sooda/thesis/latex/tex/syms-opers-abbrs.tex

\mysection{Symbols and abbreviations}

\subsection*{Symbols}

In general, bold capital letters (e.g., $\bm A$) represent matrices, plain capital letters represent 3D points and corresponding lowercase letters matching 2D points (e.g., $\vec P$, $\vec p$).
The arrow denotes a vector.
Plain letters without the arrow represent scalars.

\begin{tabular}{ll}
	$\vec C$ & camera position\\
	$f$ & focal length\\
	$\kappa_i$ & $i$th radial distortion coefficient\\
	$\bm K$ & camera intrinsic matrix\\
	$\bm M$ & projection matrix\\
	$\bm O$ & coordinate system origin\\
	$\vec p = (p_x, p_y)$ & pixel coordinates matching $\vec P$\\
	$\vec P = (P_x, P_y, P_z)$ & 3D world coordinates\\
	$\rho_i$ & $i$th tangential distortion coefficient\\
	$r$ & radius\\
	$\bm R$ & rotation matrix\\
	$t$ & time\\
	$\bm T$ & translation matrix\\
	$\vec T$ & translation vector\\
\end{tabular}
%
%\subsection*{Operators}
%
%\begin{tabular}{ll}
%$\sum_i $                        & sum over all indices $i$\\
%$\mathbf{a} \cdot \mathbf{b}$    & Dot product of the vectors $\mathbf{a}$ and $\mathbf{b}$
%\end{tabular}

\subsection*{Abbreviations}

\begin{tabular}{ll}
	2D & two-dimensional\\
	3D & three-dimensional\\
	API & Application programming interface\\
	APS-C & Advanced Photo System type-C\\
	b & bit\\
	B & byte\\
	BRDF & Bidirectional reflectance distribution function\\
	CCD & Charge-coupled device\\
	CG & Computer graphics\\
	CMOS & Complementary metal-oxide semiconductor\\
	COC & Circle of confusion\\
	CPU & Central processing unit\\
	DOF & Depth of field\\
	DSLR & Digital SLR\\
	Exif & Exchangeable image file format\\
	FPS & Frames per second\\
	GCC & Gnu compiler collection\\
	GPU & Graphics processing unit\\
	I/O & Input/Output\\
	IC & Integrated circuit\\
	LED & Light-emitting diode\\
	MCU & Microcontroller unit\\
	MILC & Mirrorless interchangeable-lens camera\\
	ML & Magic Lantern\\
	Mocap & Motion capture\\
	MP & Megapixels\\
	MTF & Modulation transfer function\\
	MV & Machine vision\\
	MVS & Multi-view stereo\\
	OpenGL & Open Graphics Library\\
	PCB & Printed circuit board\\
	PCL & Point Cloud Library\\
	px & pixel\\
	RAM & Random-access memory\\
	RGB & Red-green-blue\\
	SD & Secure Digital\\
	SDK & Software development kit\\
	SfM & Structure from motion\\
	SIFT & Scale-invariant feature transform\\
	SLR & Single-lens reflex camera (system camera)\\
	UI & User interface\\
	USB & Universal Serial Bus\\
\end{tabular}
