sooda/thesis/src/gphoto-tether/interesting-settings.txt

# this file is manually processed from --list-all-config
# the lines starting with / are special, used with readconfig.sh. they
# are the ones that are rewritten to other cameras from the selected cam

#/main/settings/capturetarget
#Label: Capture Target
#Type: RADIO
#Current: Internal RAM
#Choice: 0 Internal RAM
#Choice: 1 Memory card

/main/imgsettings/imageformat
Label: Image Format
Type: RADIO
Current: Smaller JPEG (S2)
Choice: 0 Large Fine JPEG
Choice: 1 Large Normal JPEG
Choice: 2 Medium Fine JPEG
Choice: 3 Medium Normal JPEG
Choice: 4 Small Fine JPEG  (S1 Fine)
Choice: 5 Small Normal JPEG (S1 Normal)
Choice: 6 Smaller JPEG (S2)
Choice: 7 Tiny JPEG (S3)
Choice: 8 RAW + Large Fine JPEG
Choice: 9 RAW

/main/imgsettings/imageformatsd
Label: Image Format SD
Type: RADIO
Current: Smaller JPEG (S2)
Choice: 0 Large Fine JPEG
Choice: 1 Large Normal JPEG
Choice: 2 Medium Fine JPEG
Choice: 3 Medium Normal JPEG
Choice: 4 Small Fine JPEG  (S1 Fine)
Choice: 5 Small Normal JPEG (S1 Normal)
Choice: 6 Smaller JPEG (S2)
Choice: 7 Tiny JPEG (S3)
Choice: 8 RAW + Large Fine JPEG
Choice: 9 RAW

/main/imgsettings/iso
Label: ISO Speed
Type: RADIO
Current: 1600
Choice: 0 Auto
Choice: 1 100
Choice: 2 200
Choice: 3 400
Choice: 4 800
Choice: 5 1600
Choice: 6 3200
Choice: 7 6400
Choice: 8 12800

/main/imgsettings/whitebalance
Label: WhiteBalance
Type: RADIO
Current: Auto
Choice: 0 Auto
Choice: 1 Daylight
Choice: 2 Shadow
Choice: 3 Cloudy
Choice: 4 Tungsten
Choice: 5 Fluorescent
Choice: 6 Flash
Choice: 7 Manual

/main/imgsettings/colortemperature
Label: Color Temperature
Type: TEXT
Current: 5200

/main/imgsettings/whitebalanceadjusta
Label: WhiteBalance Adjust A
Type: RADIO
Current: 0
Choice: 0 -9
Choice: 1 -8
Choice: 2 -7
Choice: 3 -6
Choice: 4 -5
Choice: 5 -4
Choice: 6 -3
Choice: 7 -2
Choice: 8 -1
Choice: 9 0
Choice: 10 1
Choice: 11 2
Choice: 12 3
Choice: 13 4
Choice: 14 5
Choice: 15 6
Choice: 16 7
Choice: 17 8
Choice: 18 9

/main/imgsettings/whitebalanceadjustb
Label: WhiteBalance Adjust B
Type: RADIO
Current: 0
Choice: 0 -9
Choice: 1 -8
Choice: 2 -7
Choice: 3 -6
Choice: 4 -5
Choice: 5 -4
Choice: 6 -3
Choice: 7 -2
Choice: 8 -1
Choice: 9 0
Choice: 10 1
Choice: 11 2
Choice: 12 3
Choice: 13 4
Choice: 14 5
Choice: 15 6
Choice: 16 7
Choice: 17 8
Choice: 18 9

/main/imgsettings/colorspace
Label: Color Space
Type: RADIO
Current: sRGB
Choice: 0 sRGB
Choice: 1 AdobeRGB

/main/capturesettings/focusmode
Label: Focus Mode
Type: RADIO
Current: Unknown value 0003
Choice: 0 One Shot
Choice: 1 AI Focus
Choice: 2 AI Servo
Choice: 3 Unknown value 0003

/main/capturesettings/drivemode
Label: Drive Mode
Type: RADIO
Current: Continuous
Choice: 0 Single
Choice: 1 Continuous
Choice: 2 Timer 10 sec
Choice: 3 Timer 2 sec
Choice: 4 Unknown value 0007

/main/capturesettings/picturestyle
Label: Picture Style
Type: RADIO
Current: Standard
Choice: 0 Auto
Choice: 1 Standard
Choice: 2 Portrait
Choice: 3 Landscape
Choice: 4 Neutral
Choice: 5 Faithful
Choice: 6 Monochrome
Choice: 7 User defined 1
Choice: 8 User defined 2
Choice: 9 User defined 3

/main/capturesettings/aperture
Label: Aperture
Type: RADIO
Current: 5
Choice: 0 1.8
Choice: 1 2
Choice: 2 2.2
Choice: 3 2.5
Choice: 4 2.8
Choice: 5 3.2
Choice: 6 3.5
Choice: 7 4
Choice: 8 4.5
Choice: 9 5
Choice: 10 5.6
Choice: 11 6.3
Choice: 12 7.1
Choice: 13 8
Choice: 14 9
Choice: 15 10
Choice: 16 11
Choice: 17 13
Choice: 18 14
Choice: 19 16
Choice: 20 18
Choice: 21 20
Choice: 22 22

/main/capturesettings/shutterspeed
Label: Shutter Speed
Type: RADIO
Current: 1/100
Choice: 0 bulb
Choice: 1 30
Choice: 2 25
Choice: 3 20
Choice: 4 15
Choice: 5 13
Choice: 6 10
Choice: 7 8
Choice: 8 6
Choice: 9 5
Choice: 10 4
Choice: 11 3.2
Choice: 12 2.5
Choice: 13 2
Choice: 14 1.6
Choice: 15 1.3
Choice: 16 1
Choice: 17 0.8
Choice: 18 0.6
Choice: 19 0.5
Choice: 20 0.4
Choice: 21 0.3
Choice: 22 1/4
Choice: 23 1/5
Choice: 24 1/6
Choice: 25 1/8
Choice: 26 1/10
Choice: 27 1/13
Choice: 28 1/15
Choice: 29 1/20
Choice: 30 1/25
Choice: 31 1/30
Choice: 32 1/40
Choice: 33 1/50
Choice: 34 1/60
Choice: 35 1/80
Choice: 36 1/100
Choice: 37 1/125
Choice: 38 1/160
Choice: 39 1/200
Choice: 40 1/250
Choice: 41 1/320
Choice: 42 1/400
Choice: 43 1/500
Choice: 44 1/640
Choice: 45 1/800
Choice: 46 1/1000
Choice: 47 1/1250
Choice: 48 1/1600
Choice: 49 1/2000
Choice: 50 1/2500
Choice: 51 1/3200
Choice: 52 1/4000

/main/capturesettings/meteringmode
Label: Metering Mode
Type: RADIO
Current: Evaluative
Choice: 0 Evaluative
Choice: 1 Partial
Choice: 2 Spot
Choice: 3 Center-weighted average

/main/capturesettings/bracketmode
Label: Bracket Mode
Type: TEXT
Current: 0

# aeb is not there when using the pop-up flash
#/main/capturesettings/aeb
#Label: Auto Exposure Bracketing
#Type: RADIO
#Current: off
#Choice: 0 off
#Choice: 1 +/- 1/3
#Choice: 2 +/- 2/3
#Choice: 3 +/- 1
#Choice: 4 +/- 1 1/3
#Choice: 5 +/- 1 2/3
#Choice: 6 +/- 2
