sooda/thesis/latex/gfx/tex/lens.tex

\documentclass{standalone}
\usepackage{tikz}
\begin{document}

\begin{tikzpicture}

% http://tex.stackexchange.com/questions/14901/dimensioning-of-a-technical-drawing-in-tikz
\tikzset{%
    dimen/.style={<->,>=latex,thin,every rectangle node/.style={fill=white,midway,font=\sffamily}},
}

%\namedhorline{text}{textpos}{radius}
\newcommand*{\namedhorline}[3]{%
	%\draw [<-] ++ -- ++(\dx,\dy) -- ++(\dx,-\dy) -- ++(-\dx,-\dy) -- cycle
	\draw [->] (#2) +(-0.2,0) -- +(-#3,0);
	\node at (#2) {#1};
	\draw [->] (#2) +(0.2,0) -- +(#3,0);
}

\def\rad{10}
\def\ang{8}

\def\lensx{0}
\def\lensy{0}
\def\lensw{0.2}

\def\objh{1}
\def\imgh{0.5}
\def\objx{6}
\def\imgx{3}
\def\f{2}
% 1/3 + 1/6 = 1/2

\def\flabely{2}
\def\alabely{3}

% background
\draw [dashed] (-\objx-1, 0) -- (\imgx+1, 0);

% lens

\draw [thick] (\lensx+\lensw/2,\lensy) arc [radius=\rad, start angle=0, end angle=\ang];
\draw [thick] (\lensx+\lensw/2,\lensy) arc [radius=\rad, start angle=0, end angle=-\ang];

\draw [thick] (\lensx-\lensw/2,\lensy) arc [radius=\rad, start angle=180, end angle=180+\ang];
\draw [thick] (\lensx-\lensw/2,\lensy) arc [radius=\rad, start angle=180, end angle=180-\ang];
%\draw (\lensx-\lensw/2,\lensy) arc [radius=\rad, start angle=180-\ang, end angle=180+\ang];

% object, image
\draw [green, ultra thick, ->] (-\objx, 0) -- (-\objx, \objh);
\draw [green, ultra thick, ->] (\imgx, 0) -- (\imgx, -\imgh);

% light beams
\draw [red] (-\objx, \objh) -- (\lensx, \lensy+\objh) -- (\imgx, -\imgh);
\draw [red] (-\objx, \objh) -- (\imgx, -\imgh); % thru the lens center
\draw [red] (-\objx, \objh) -- (\lensx, \lensy-\imgh) -- (\imgx, -\imgh);

% labels

\draw (0, 0) -- ++(0, \alabely);

\draw (-2, 0) -- ++(0, \flabely) coordinate (Df);
\draw (2, 0) -- ++(0, \flabely) coordinate (Dff);
\draw [dimen] (Df) -- ++(\f, 0) node {$f$};
\draw [dimen] (Dff) -- ++(-\f, 0) node {$f$};

%\namedhorline{a}{-3,\alabely}{3}
\draw (-\objx, \objh) -- (-\objx, \alabely) coordinate (Da);
\draw [dimen] (Da) -- ++(\objx, 0) node {$a$};

\node at (-\objx, -1) {subject};
\node at (\imgx, -1) {image};

%\namedhorline{b}{1.5,\alabely}{1.5}
\draw (\imgx, 0) -- ++(0, \alabely) coordinate (Db);
\draw [dimen] (Db) -- ++(-\imgx, 0) node {$b$};

\end{tikzpicture}

\end{document}
