sooda/thesis/semma/presis/presis.pdf

## Non-static object capture using multi-view stereo video

Konsta Hölttä

AS-0.3100 seminar presentation konsta.holtta@aalto.fi

Apr 25, 2014

MVS non-static capture
Apr 25, 2014
2/22

## non-static object capture using multi-view stereo video

I Non-static / dynamic: moving or morphing over time I ⇒ video, maybe not just a simple object
I object: some target of interest in front of a camera
I capture: encode the object’s visual properties digitally I geometry: 3d surface structure
I texture: (diffuse) color
I multi-view stereo: recover 3D from photographs
I video: a sequence of frames

this presentation reviews the parts of the capture pipeline

3/22

## Contents

I Intro, motivation
I Imaging basics
I Stereo reconstruction
I Motion specifics
I Post processing
I Conclusion

4/22

## Motivation

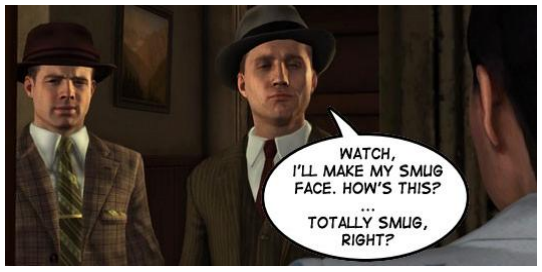
[picture p41: figure]

L.A. Noire / joystiq.com
I applications in mapping, object replication, entertainment, cultural heritage, medical, crime investigation, ...
I most visible in modern movies and video games
I facial expressions; motion/surface capture
I relatively cheap hardware

5/22

## Cameras

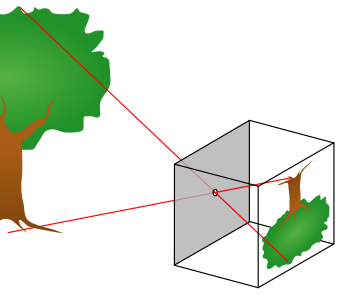
[picture p42: figure]

Pinhole camera projects an image perfectly (and rotated upside down)
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
## Real cameras

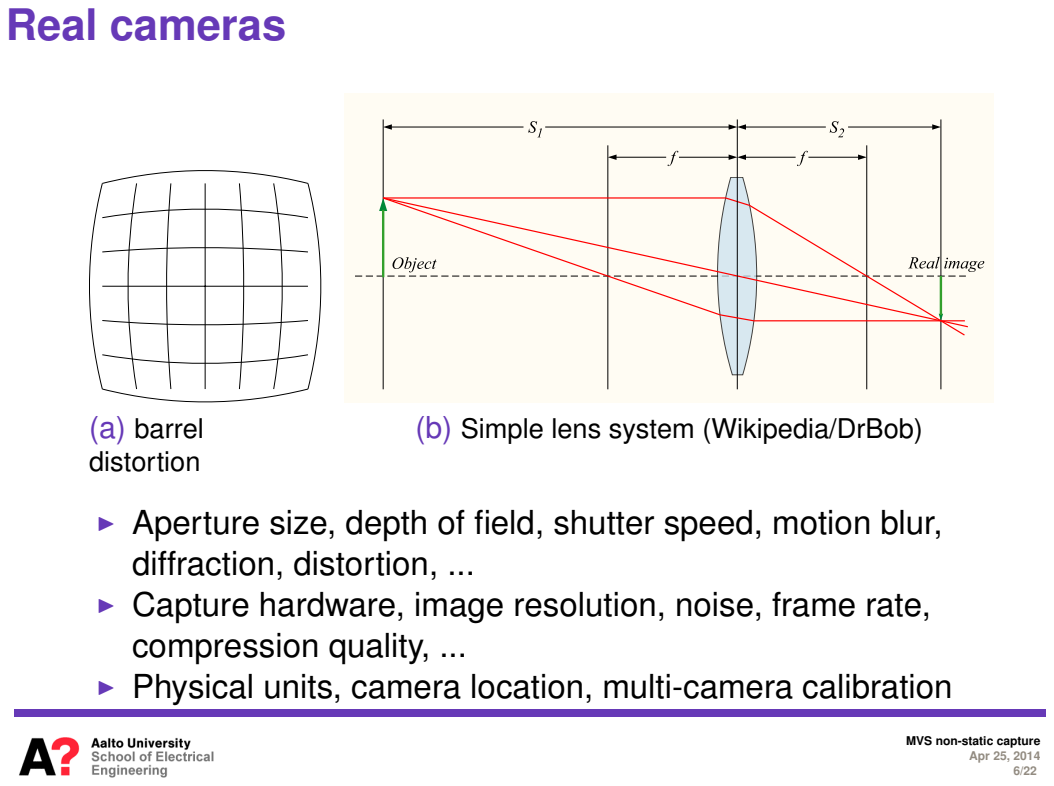
[picture p43: page 6]
(a) barrel distortion

(b) Simple lens system (Wikipedia/DrBob)

I Aperture size, depth of field, shutter speed, motion blur,
diffraction, distortion, ...
I Capture hardware, image resolution, noise, frame rate,
compression quality, ...
I Physical units, camera location, multi-camera calibration

7/22

## Video concerns

0te | 1t | 2t | 3t | 4t | 5t

cam A

cam B

I Lighting
I Motion blur
I Rolling shutter
I Sub-frame synchronization
I Other issues (23.97(6) FPS, mechanics, wiring, ..)

8/22

## Calibration, camera parameters

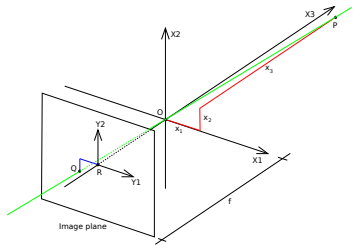
[picture p44: figure]
Image plane

αx f | γ | u0
0 | αy f v0
0 | 0 | 1

I Given known 3D coordinates and corresponding images, what is the projection matrix? (intrinsics, extrinsics)
I Done for single cameras and camera systems
I Projections closely related to computer graphics in general

9/22

## (Multi view) stereo

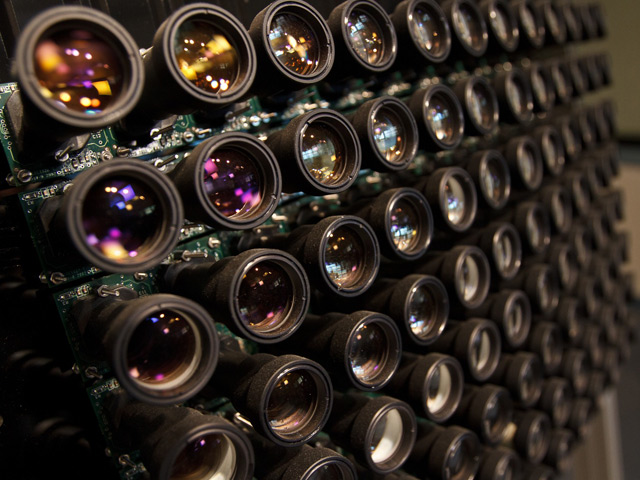
[picture p45: figure]

Stanford camera array.
Several cameras imaging the same scene at the same time

10/22

## Disparity in stereo vision

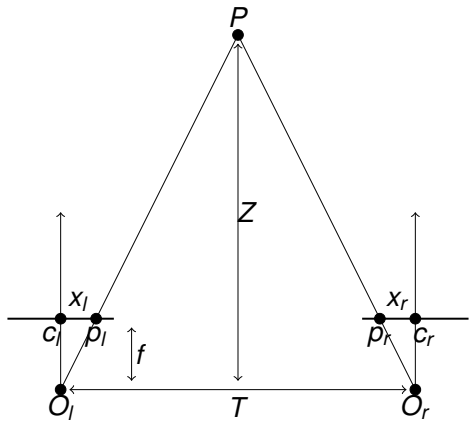
[picture p46: figure]

Two identical cameras; depth inversely related to xr − xl , i.e.
pixel disparity between corresponding points in images

11/22

## Epipolar geometry

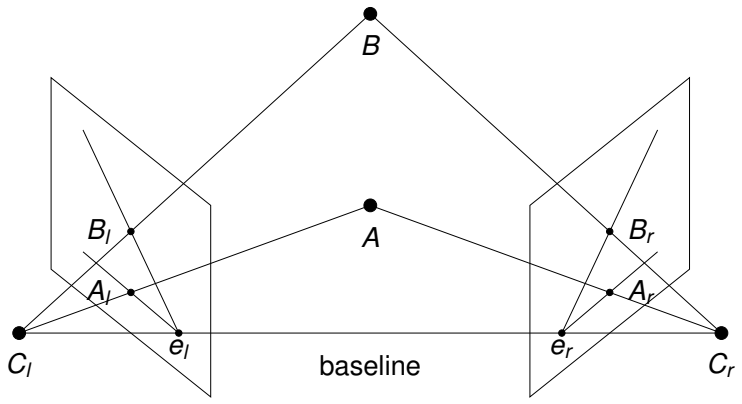
[picture p47: figure]
baseline

Corresponding points are found on lines. Rectification twists the images so that those lines become horizontal (or vertical).

12/22

## Really multi-view

I Two camera case is still pretty dull
I Combine pairs, reconstruct individually, register in 3d
I Several on same baseline, match pairwise, fit least errors I Use lots, arbitrarily positioned; magic algorithms
I Single camera traversing in a scene (SfM)

13/22

## From static to dynamic

I Static can be scanned with a single camera only
I Moving targets need static frames from many angles I Images must be consistent within a frame
I Stream of static frames reconstructed, or more sophisticated tracking

14/22

## Dynamic methods

I Brute force reconstruction of every video frame I Register together, build a mesh while going
I Morph initial model based on frame deformations
I Track local pre-selected features in 2D
I Track features in 3D, deform mesh based on keypoints
I And more and more post-processing, assumptions on the object properties

15/22

## Texture and topology

I Reconstruction outputs local geometry properties
I Color per vertex, not textured, not meshed
I Reconstruct surface topology: fit data to surface, fill holes; use models
I Reproject camera views on ready mesh to recover texture maps
I Sometimes features tracked in 2D or 3D (still pre-recorded) I Feature spaces and parameterizations in extreme cases

16/22

## In practice

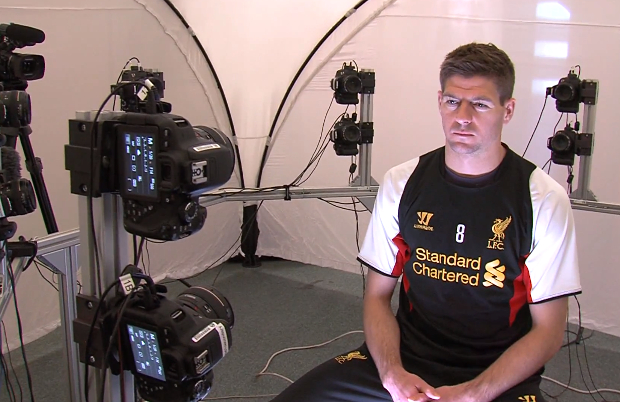
[picture p48: figure]

(EA sports, FIFA ’14; 18 DSLRs) I Shutter delay and jitter, flash sync, remote control
I construction issues, calibration convenience, bad software, ...
I Manual work for artists, 3D noise removal, magic coefficients

17/22

## Software

I Libs: OpenCV, Point Cloud Library, Computational Geometry Algorithms Library, ...
I Free: Camera calibration toolbox for Matlab (+OpenCV), Bundler, Sift, SiftGPU, PBA, PMVS/CMVS, VisualSFM, Meshlab, PoissonRecon, CmpMVS, Python photogrammetry toolbox, ...
I Commercial: Photosynth, 123D Catch, Agisoft PhotoScan, CaptiveMotion, DI3D, MotionScan, Faceshift, 3DF Zephyr Pro, Mova Contour Reality Capture, Pendulum Studio, Pix4DMapper, Acute3D, ...

4D programs very customized

18/22

## VisualSFM

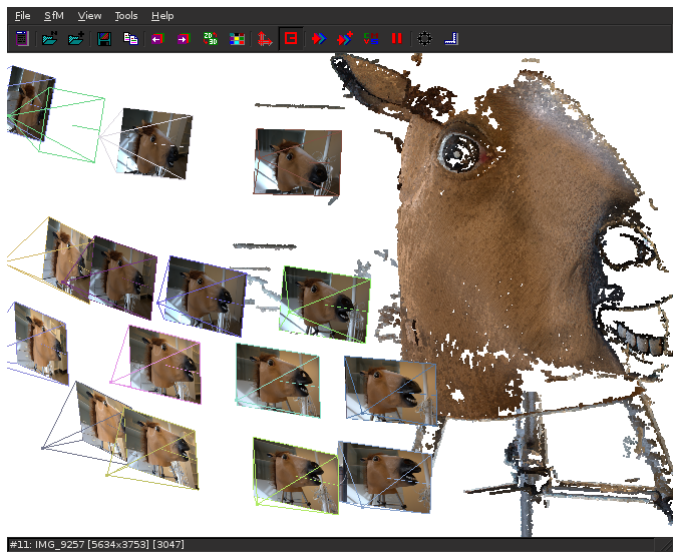
[picture p49: figure]

19/22

## Meshlab

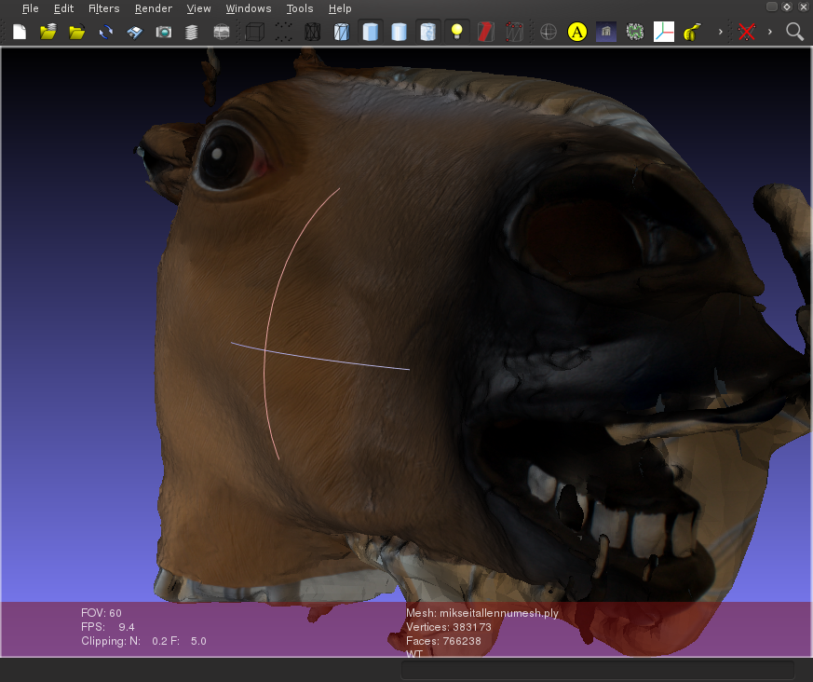
[picture p50: figure]

20/22

## Meshlab

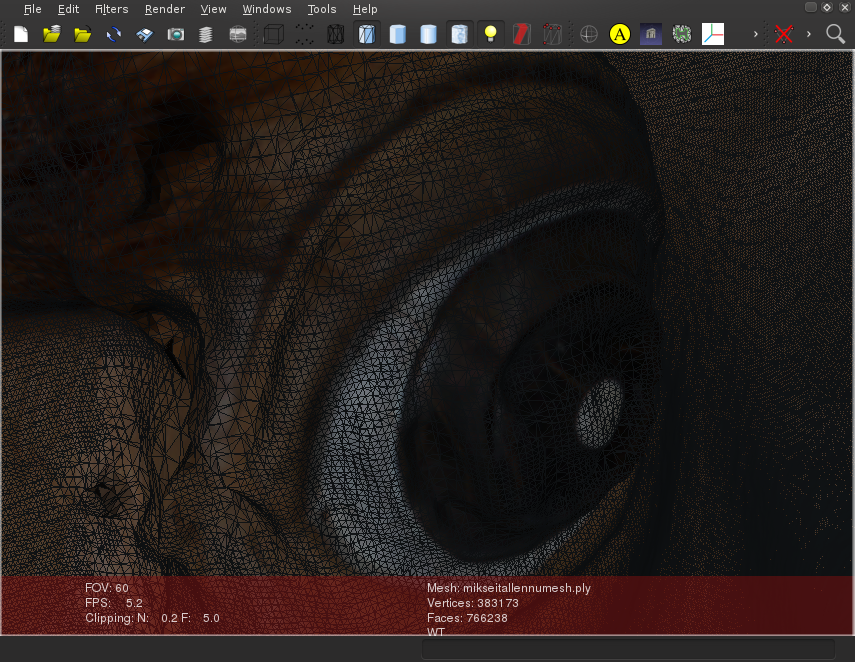
[picture p51: figure]

21/22

## Meshlab

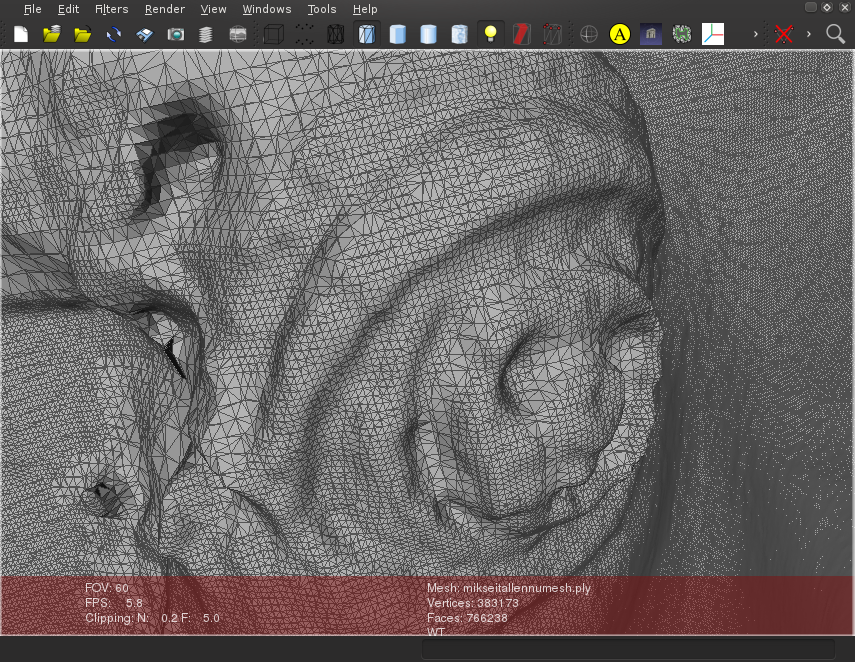
[picture p52: figure]

22/22

## Conclusion

I 4D scan: multi-step pipeline from construction to shooting, reconstruction and post-processing
I Used method(s) largely application specific
I Lots of software, special applications coming, rising trend I MVS just one scanning method

Many tools integrate some steps or add in their own
