sooda/thesis/latex/dippa.tex

% XXX \baselineskip
\documentclass[english,12pt,a4paper,pdftex]{article}
%\documentclass[english,12pt,a4paper,dvips]{article}
% wat? using additionally finnish here would hyphenate the abstract page properly, but would also change some titles to finnish. maybe a bug in aaltothesis.sty?
%\usepackage[english,finnish]{babel}
%\PassOptionsToPackage{finnish}{babel}
\usepackage[elec,utf8]{aaltothesis}

% render without images:
% \renewcommand{\includegraphics}[2][]{\fbox{#2}}

% pdflatex, gfx in jpg/pdf
\usepackage{graphicx}
%\usepackage{url}
\PassOptionsToPackage{hyphens}{url}
\usepackage[pdfpagemode=None,colorlinks=true,urlcolor=red,%
linkcolor=blue,citecolor=black,pdfstartview=FitH]{hyperref}
\usepackage[comma,sort&compress,numbers]{natbib}

\usepackage{amsfonts,amssymb,amsbsy,amsmath}
\usepackage{tikz}

% flush floats without forcing a partly clear page
\usepackage{afterpage}

% (ugly) euro symbol from €
\usepackage[official]{eurosym}
\DeclareUnicodeCharacter{20AC}{\euro{}}
%or:
%\usepackage{marvosym}
%\DeclareUnicodeCharacter{20AC}{\EUR{}}
\usepackage{textcomp}

% micro sign µ
\usepackage{siunitx}
\sisetup{math-micro=\text{µ},text-micro=µ}

% bold math
\usepackage{bm}

%\usepackage{draftwatermark}
%\SetWatermarkText{DRAFT}
%\SetWatermarkScale{3.33}
%\SetWatermarkColor{gray!20}

\usepackage{listings}

\input{gfx/tex/bayer}
% \simplefig{pos-specifier}{contents}{labelname}{caption}
\newcommand{\simplefig}[4]{%
	\begin{figure}[#1]\centering
		#2
		\caption{#4}
		\label{#3}
	\end{figure}
}
% \simplegfx{pos-specifier}{width}{filename-and-labelname}{caption}
\newcommand{\simplegfx}[4]{%
	\simplefig{#1}{}{fig:#3}{#4}
}

\setlength{\hoffset}{-1in}
\setlength{\oddsidemargin}{35mm}
\setlength{\evensidemargin}{25mm}
\setlength{\textwidth}{15cm}

\setlength{\voffset}{-1in}
\setlength{\headsep}{7mm}
\setlength{\headheight}{1em}
\setlength{\topmargin}{25mm-\headheight-\headsep}
\setlength{\textheight}{23cm}

% \frenchspacing

\graphicspath{ {gfx/tex/}{gfx/dot/}{gfx/bitmap/}{gfx/vector/} }

\begin{document}

\department{Department of Electrical Engineering and Automation}%
{Sähkötekniikan ja automaation laitos}
\professorship{Automation technology}{Automaatiotekniikka}
\code{AS-84}

\univdegree{MSc}

\author{Konsta Hölttä}

% a rig for multi-view stereo reconstruction of facial movement
% multi-view stereo image acquisition rig for face reconstruction/content generation
% multi-view stereo reconstruction/acquisition for (realistic) 3d/computer graphics content generation/capture

% multi-view stereo reconstruction for computer graphics content capture
% monen näkymän stereon rekonstruktio tietokonegrafiikan sisällön taltiointiin
\thesistitle{Multi-view stereo reconstruction for computer graphics content capture}{Monen näkymän stereon rekonstruktio tietokonegrafiikan sisällön taltiointiin}

\place{Espoo}
\date{18.5.2015}

\supervisor{Prof.~Ville Kyrki}{Prof.~Ville Kyrki}
\instructor{Prof.~Jaakko Lehtinen}{Prof.~Jaakko Lehtinen}

\uselogo{aaltoPurple}{!}

\makecoverpage

\include{tex/abstract}
\include{tex/preface}
\newpage

\thesistableofcontents

\include{tex/syms-opers-abbrs}

\cleardoublepage
\storeinipagenumber
\pagenumbering{arabic}
\setcounter{page}{1}

\include{tex/introduction}
\include{tex/background}
\include{tex/materials-methods} % / design+integration / system implementation / more custom subsections
\include{tex/results} % / results+verification
\include{tex/summary} % / conclusions

\phantomsection
\addcontentsline{toc}{section}{References}
\bibliographystyle{unsrt}
\bibliography{dippa}

\appendix
\clearpage
% liitteet
%\phantomsection

\input{tex/appendix}

\end{document}
