sooda/thesis/latex/tex/preface.tex

\mysection{Preface}
This thesis is the first step in an adventure that started from a need and interest for an end-to-end machinery for acquiring realistic 3D content for computer graphics research and content production in Aalto University.
The work was conducted in the Department of Media Technology at Aalto University, with help from the Automation Technology laboratory.
My personal field of study and greatest interest is Automation and Systems Technology, where similar applications of computer vision can be found in robotics.

I would like to thank my advisor Jaakko Lehtinen for his guidance regarding this work and for the glorious opportunity to work on such an interesting subject, and my supervisor Ville Kyrki for valuable and supportive feedback on this thesis.
Thanks too to my co-workers at the time, Markus Kettunen, Miika Aittala and Ari Silvennoinen, for inspiring discussions about computer graphics during this work.

Last but not least, thanks also to my family and friends for all the help and support.
Of them, special greetings to Arto Rusanen and Samuli Vuorinen for sharing their deep knowledge in imaging technology and lending me photography hardware.
Arto also kindly worked as a test subject.

\vspace{5cm}
Otaniemi, 18.5.2015

\vspace{5mm}
{\hfill Konsta ``sooda'' K.\ Hölttä \hspace{1cm}}
