sooda/thesis/finalpresis/gfx/pinhole-camera.pdf

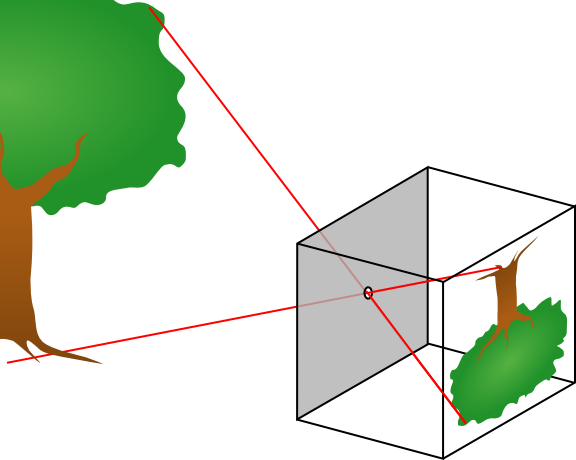
[picture p53: figure]
