sooda/thesis/finalpresis/gfx/pinhole3d.pdf

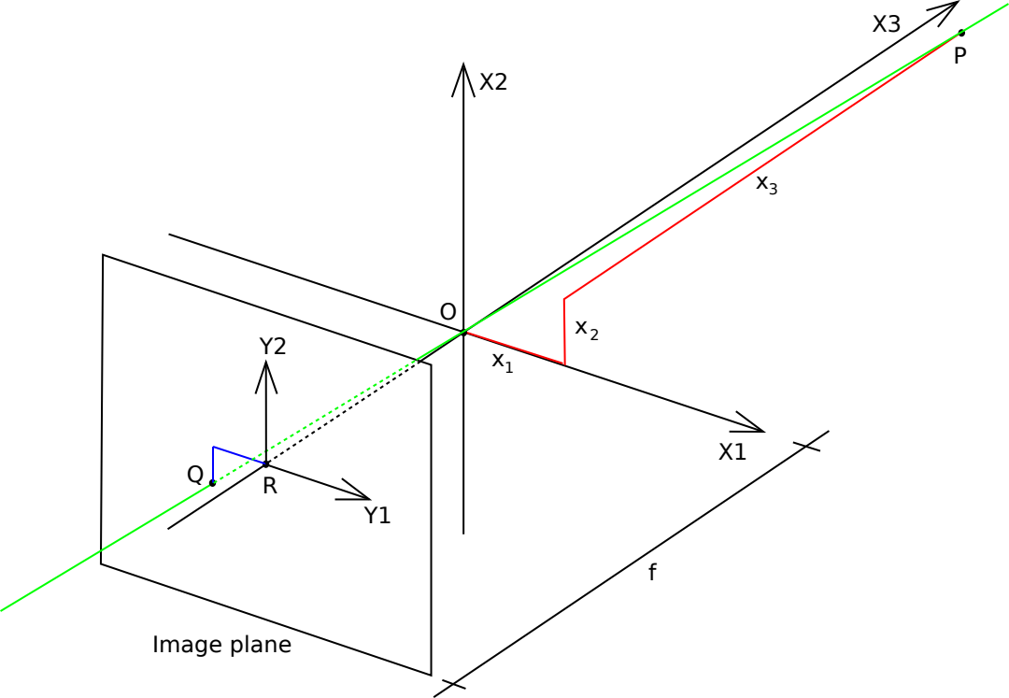
[picture p54: figure]
Image plane
