sooda/thesis/latex/gfx/vector/pinhole3d.pdf

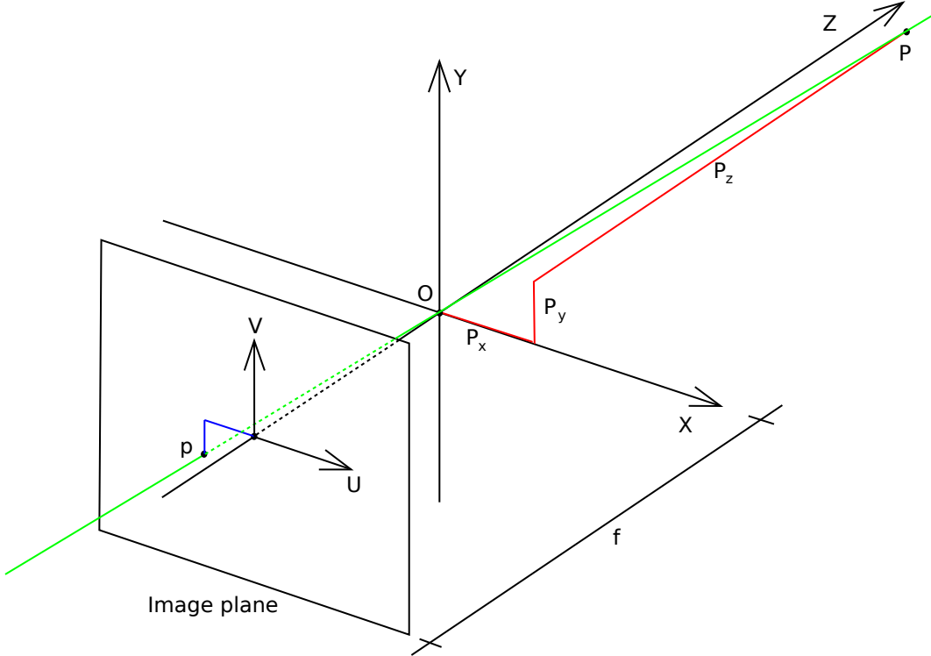
[picture p55: figure]
Image plane
