sooda/thesis/latex/gfx/vector/rectification.pdf

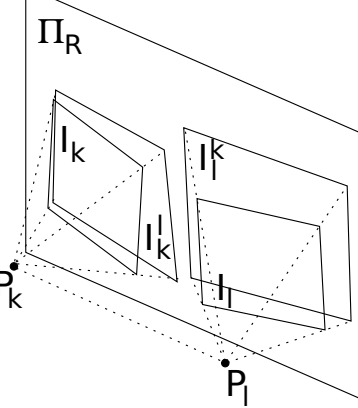
[picture p56: figure]

P
