sooda/thesis/latex/gfx/vector/perspproj.pdf

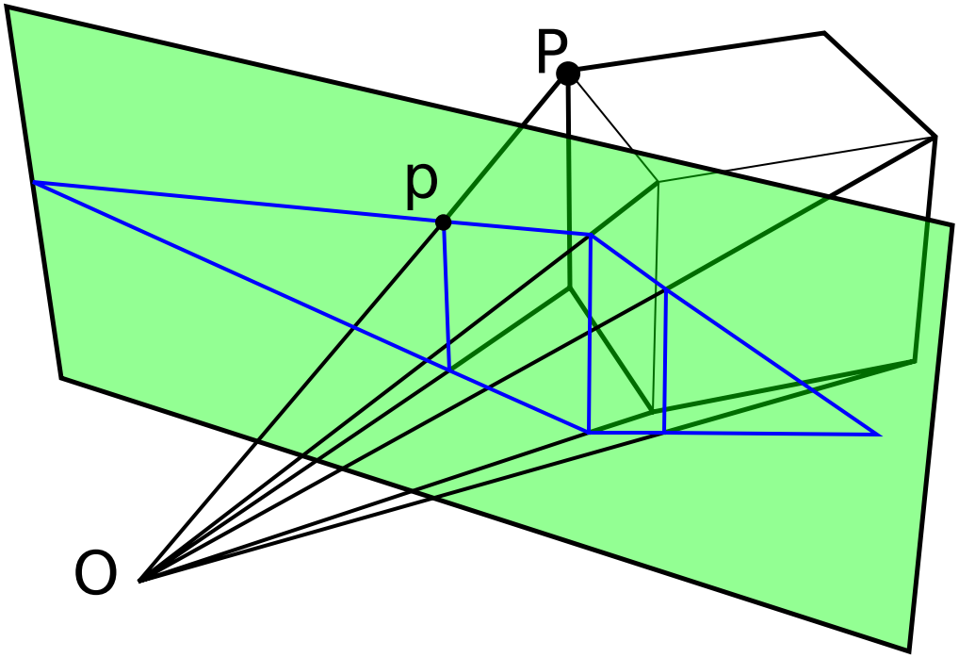
[picture p57: figure]
