sooda/thesis/latex/gfx/vector/projxformworld.pdf

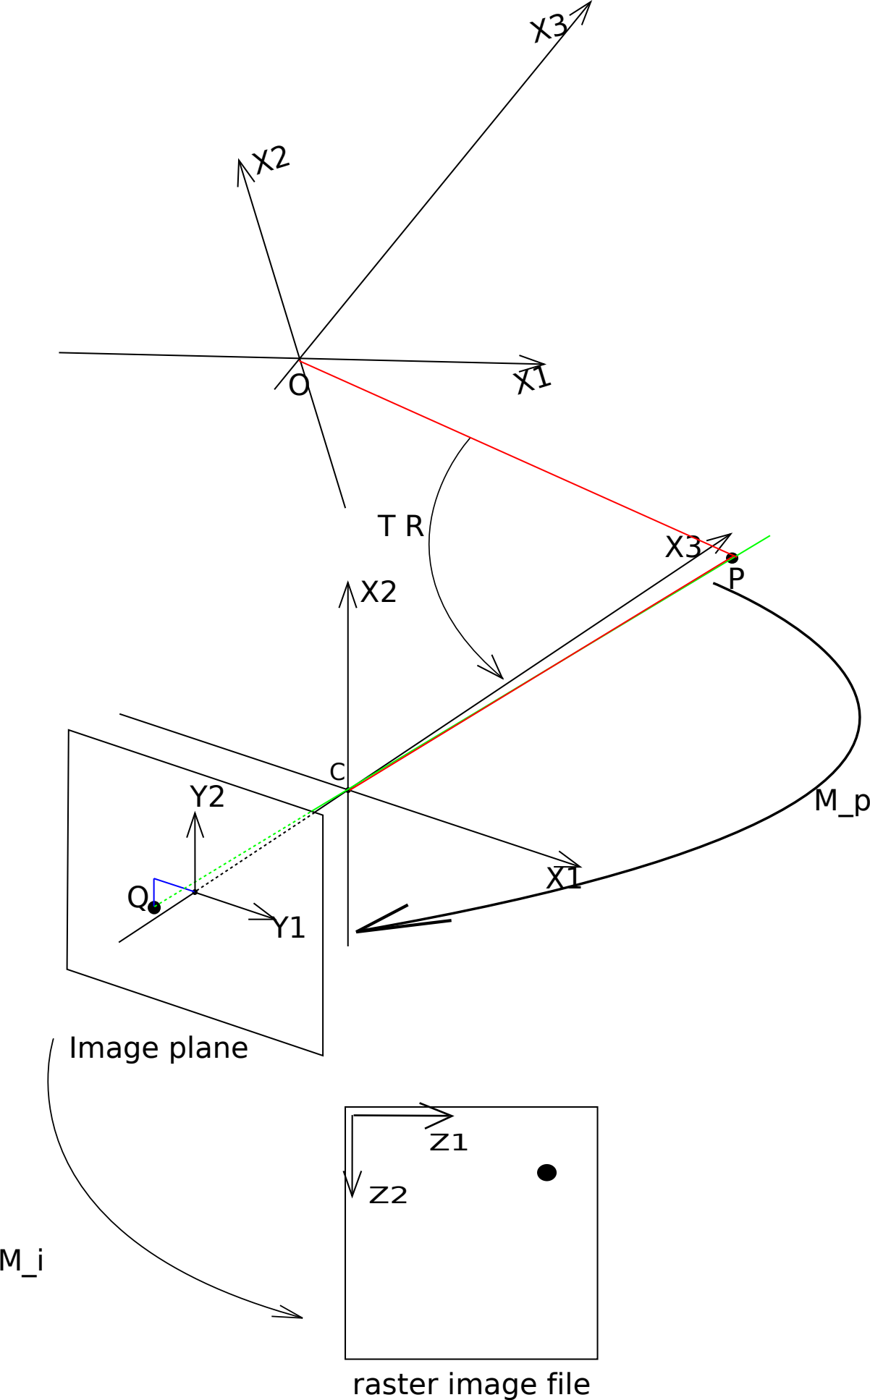
[picture p58: figure]
Image plane; raster image file
