sooda/thesis/latex/gfx/vector/rectif.pdf

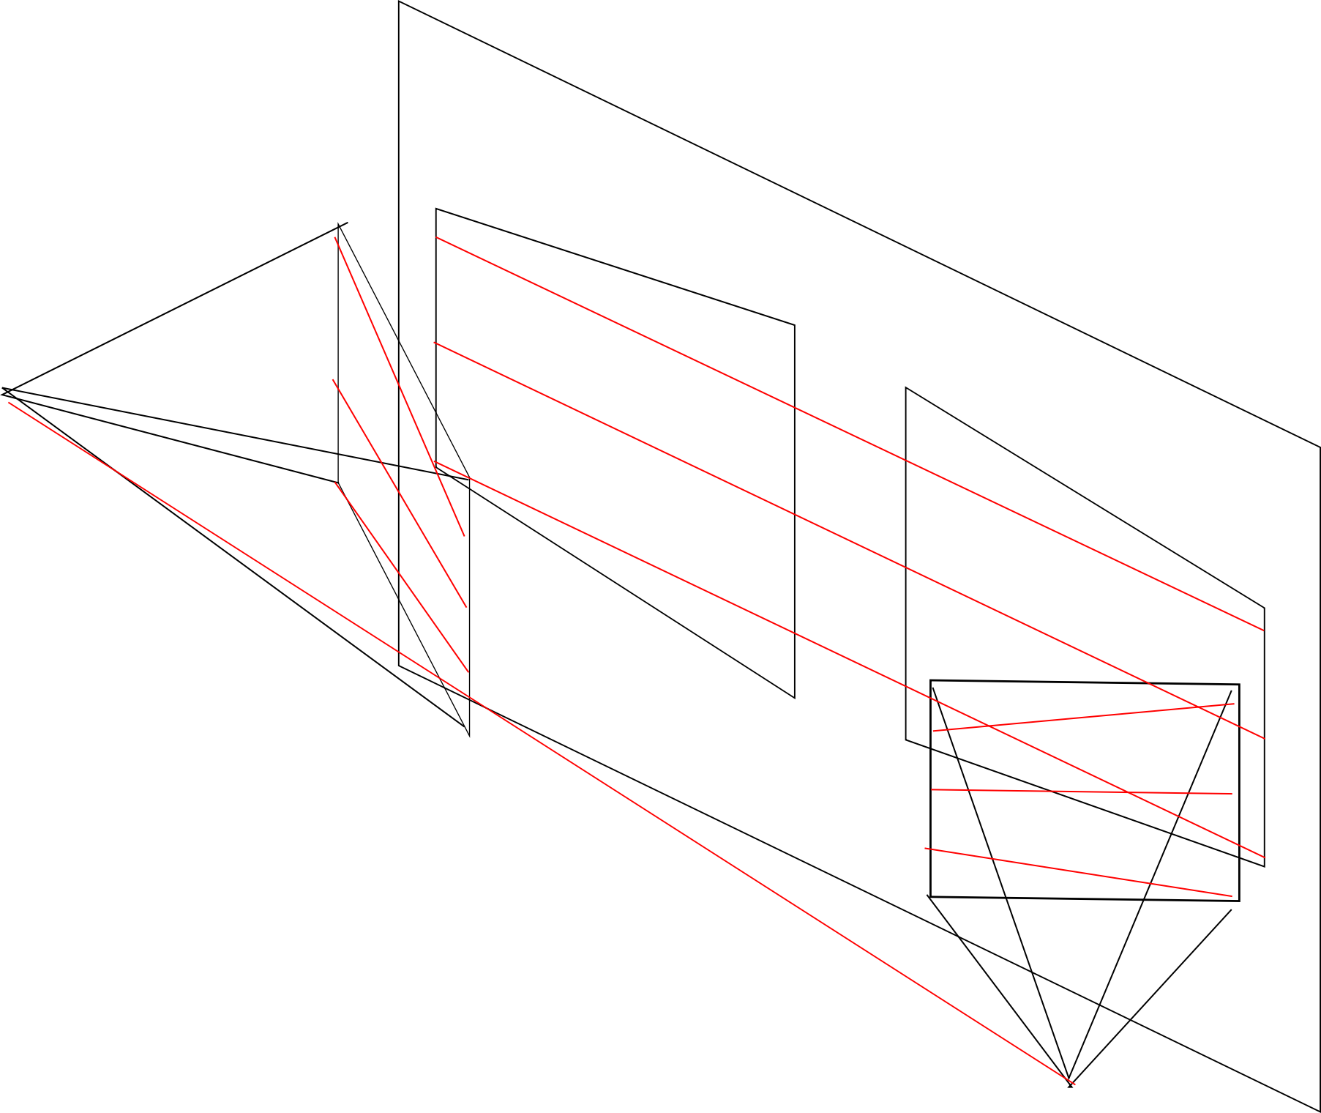
[picture p59: figure]
