sooda/thesis/semma/presis/gfx/pinhole-camera.pdf

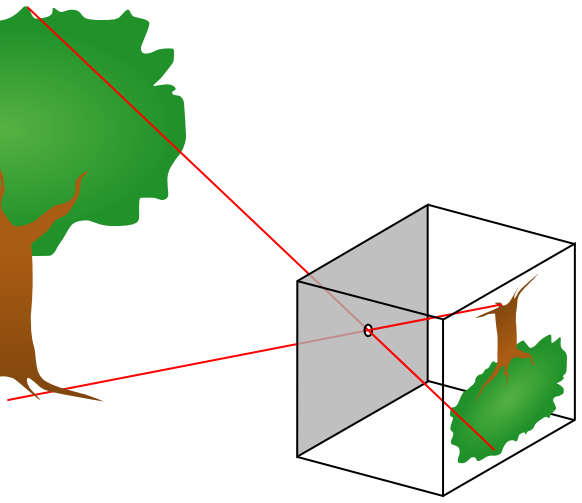
[picture p60: figure]
