sooda/thesis/finalpresis/gfx/ira-eyes.jpg

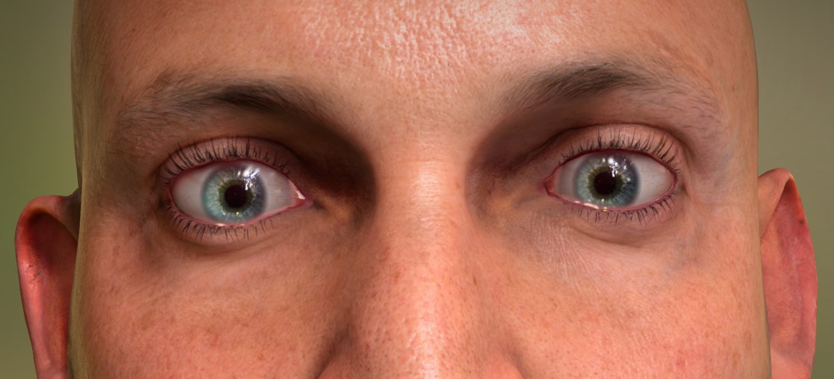
finalpresis/gfx/ira-eyes.jpg
