sooda/thesis/finalpresis/gfx/soodaheadreconsteyeswire.jpg

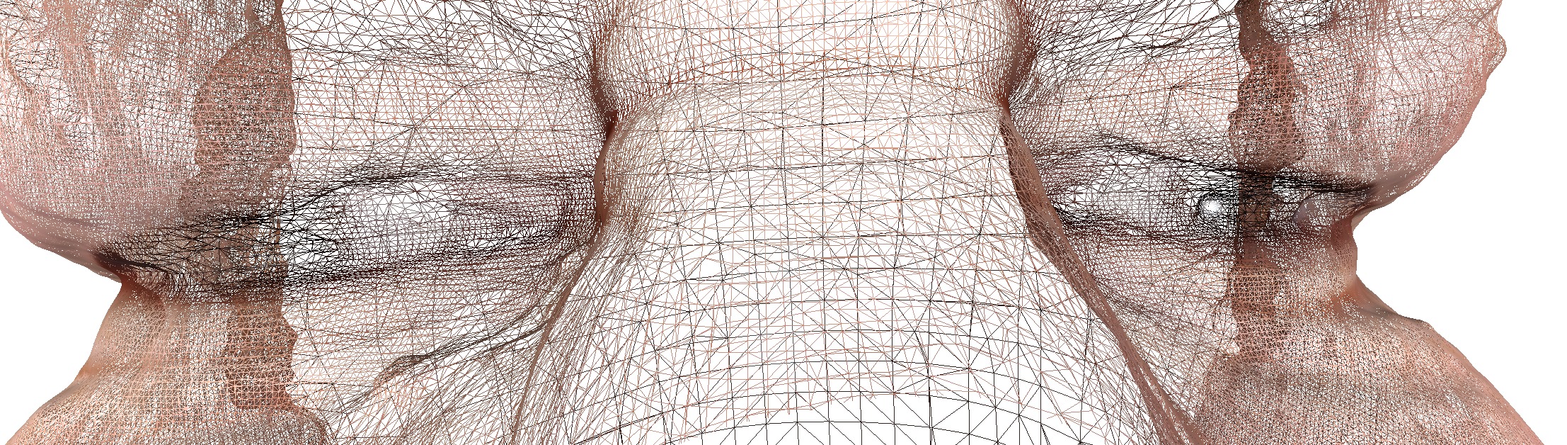
finalpresis/gfx/soodaheadreconsteyeswire.jpg
