sooda/thesis/latex/gfx/bitmap/arto-dense-close-solid.png

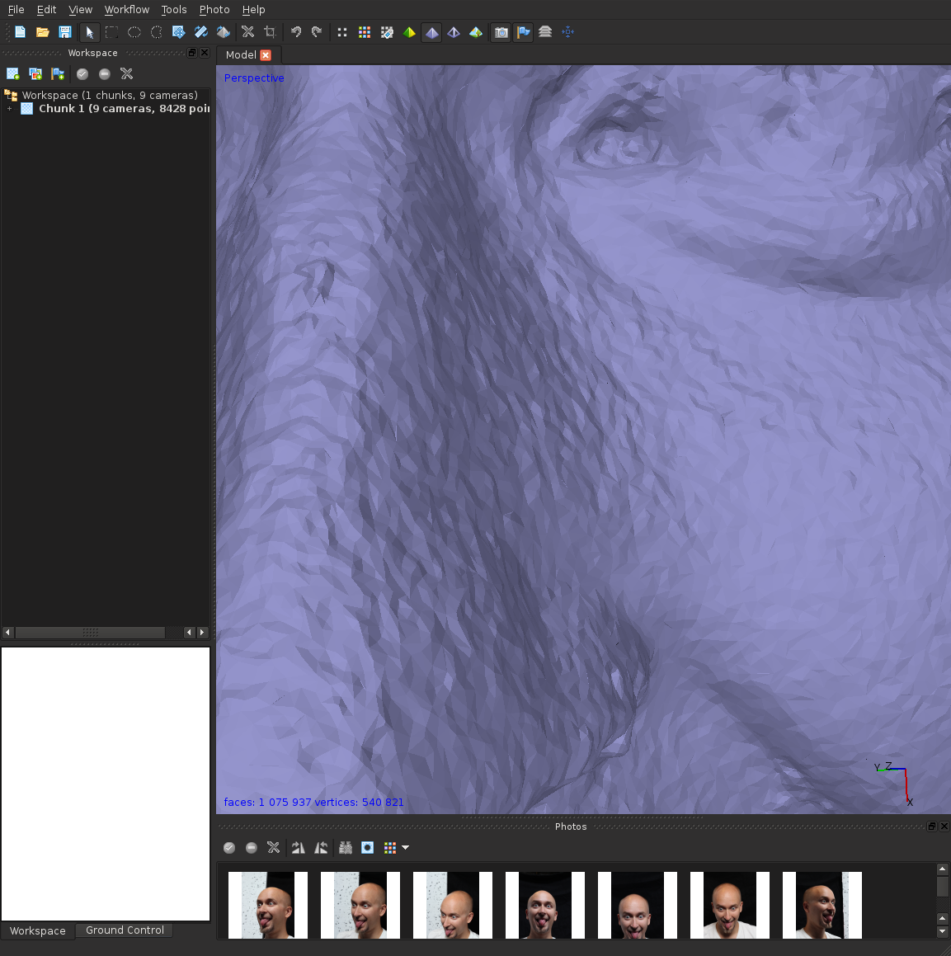
latex/gfx/bitmap/arto-dense-close-solid.png
