sooda/thesis/latex/gfx/bitmap/arto-dense-close-tex.png

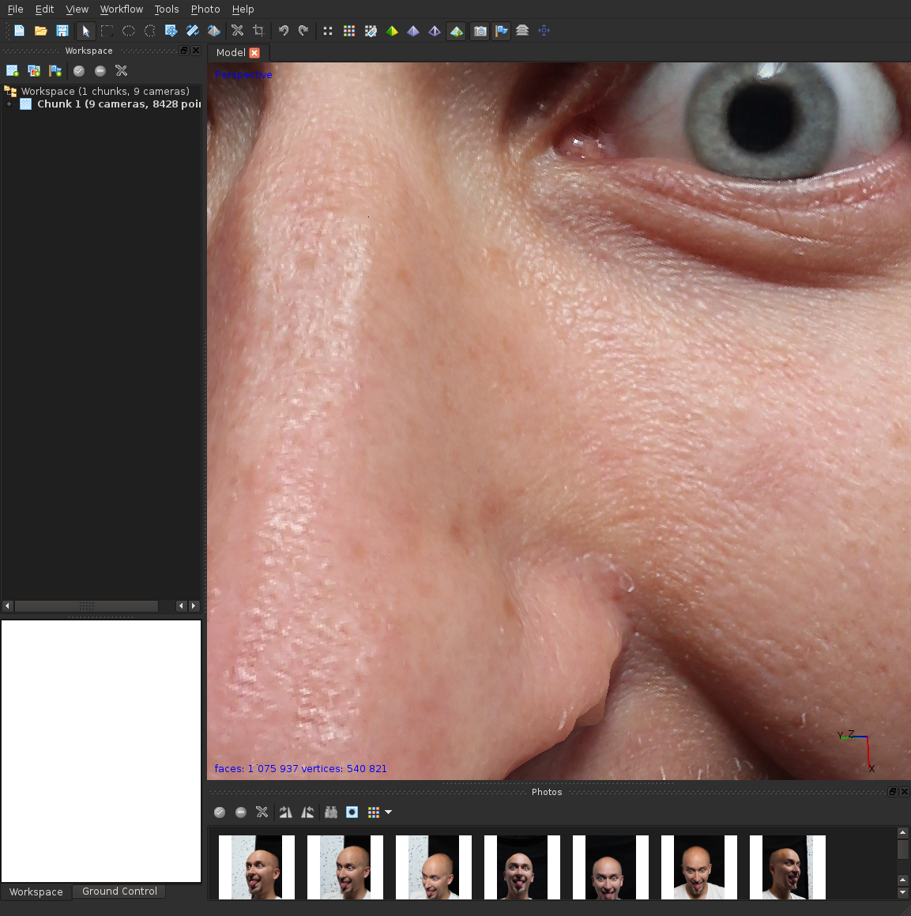
latex/gfx/bitmap/arto-dense-close-tex.png
