sooda/thesis/latex/gfx/bitmap/arto-forehead-dense.png

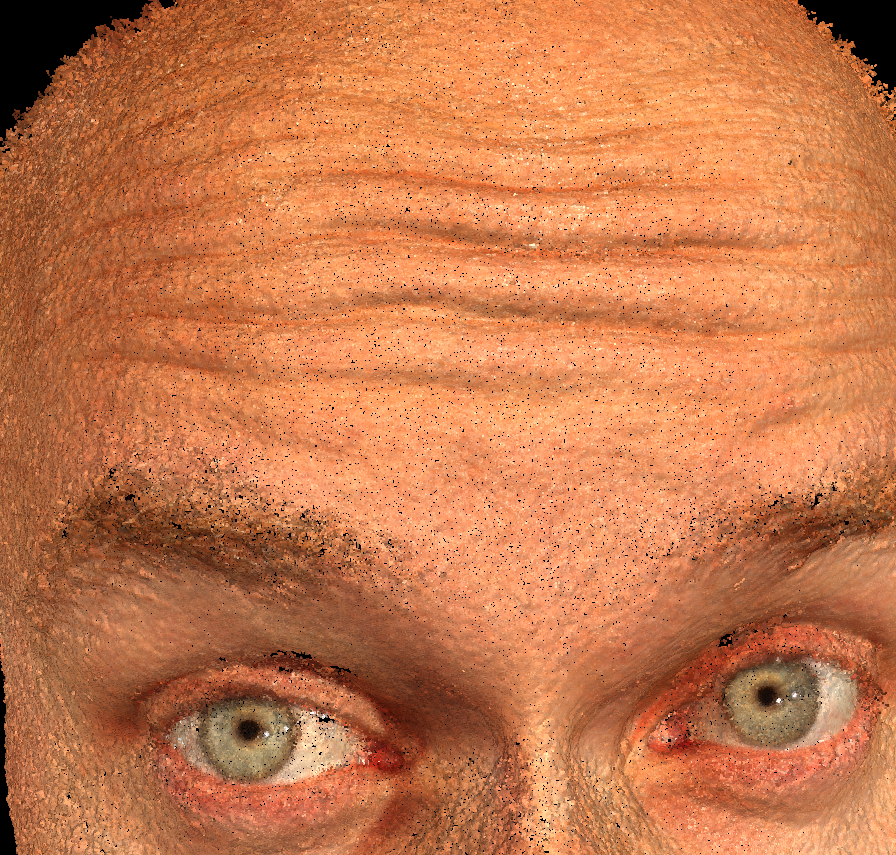
latex/gfx/bitmap/arto-forehead-dense.png
