sooda/thesis/latex/gfx/bitmap/arto-forehead-solid.png

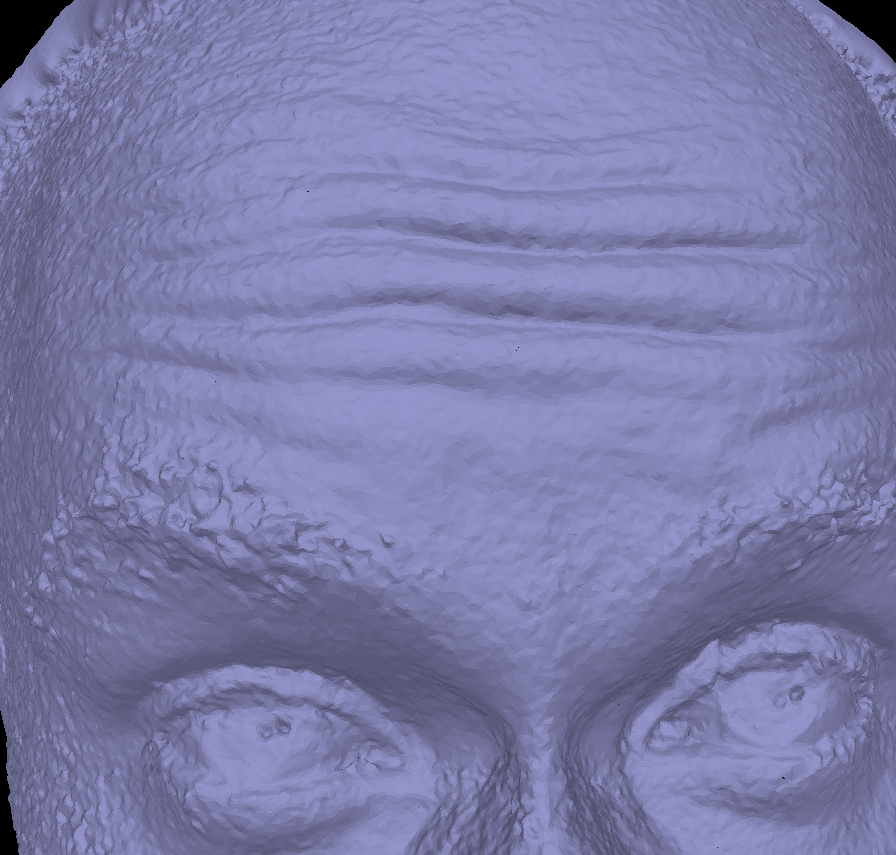
latex/gfx/bitmap/arto-forehead-solid.png
