sooda/thesis/latex/gfx/bitmap/arto-forehead-tex.png

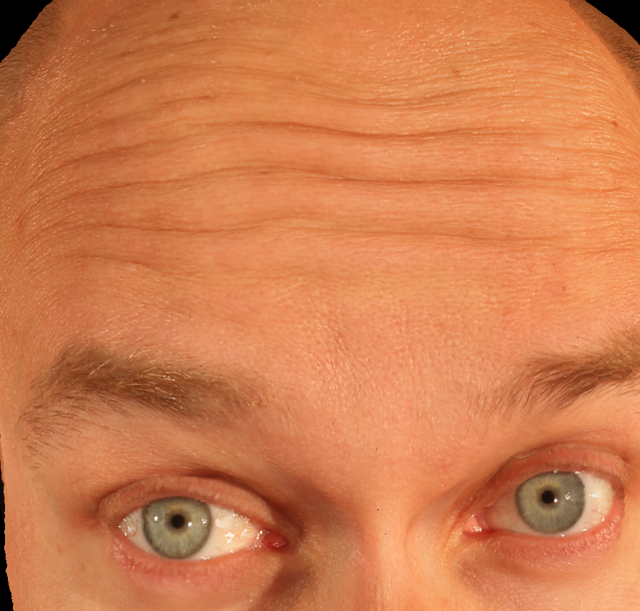
latex/gfx/bitmap/arto-forehead-tex.png
