sooda/thesis/latex/gfx/bitmap/arto-forehead-uvmap.png

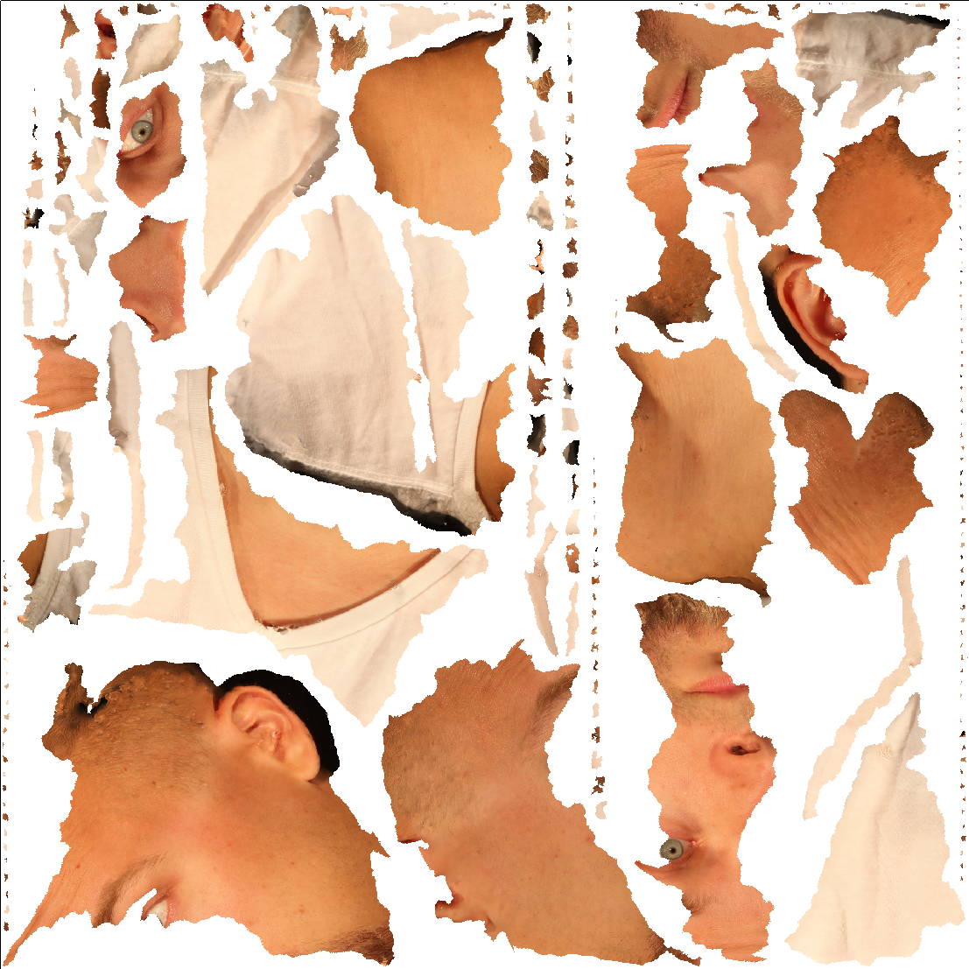
latex/gfx/bitmap/arto-forehead-uvmap.png
