sooda/thesis/latex/gfx/bitmap/arto-forehead-wireframe.png

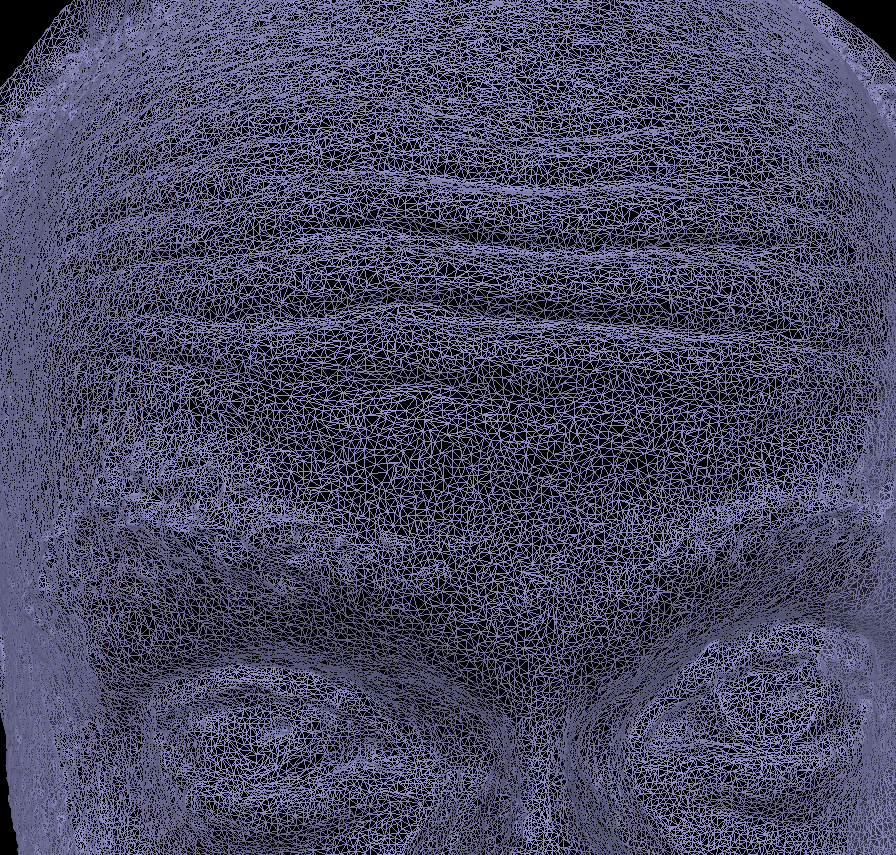
latex/gfx/bitmap/arto-forehead-wireframe.png
