sooda/thesis/latex/gfx/bitmap/artoheppa-kuono-solid.jpg

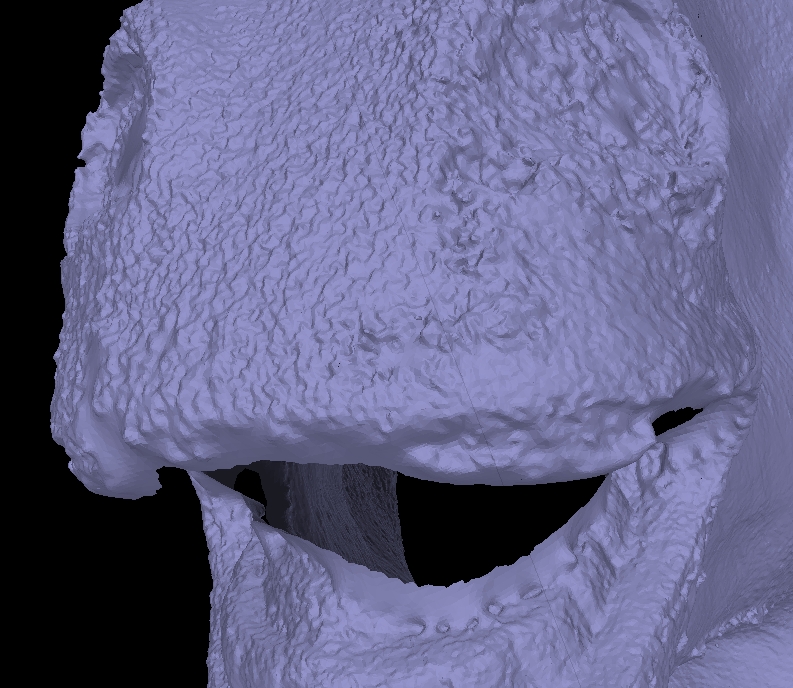
latex/gfx/bitmap/artoheppa-kuono-solid.jpg
