sooda/thesis/latex/gfx/bitmap/artoheppa-kuono-tex.jpg

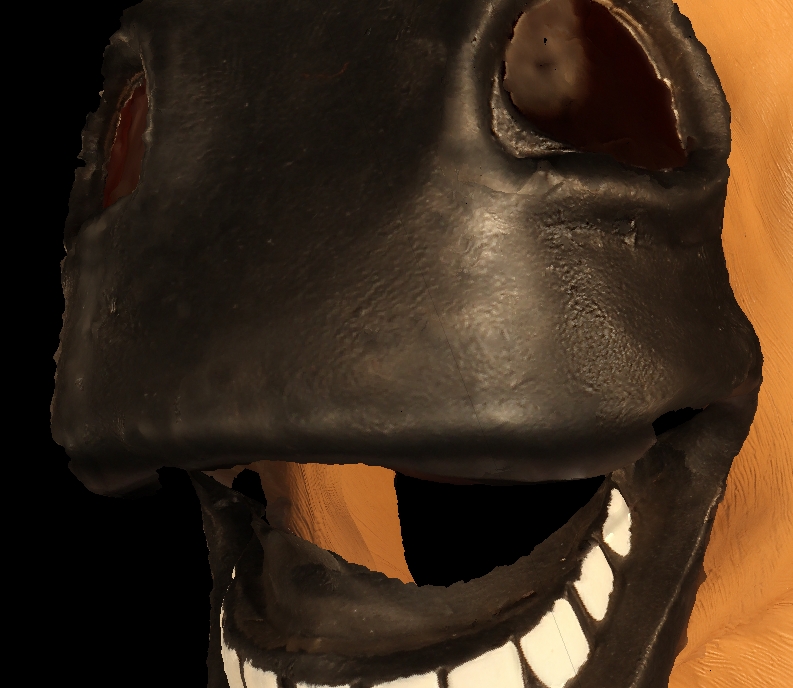
latex/gfx/bitmap/artoheppa-kuono-tex.jpg
