sooda/thesis/latex/gfx/bitmap/brdfdiagram.png

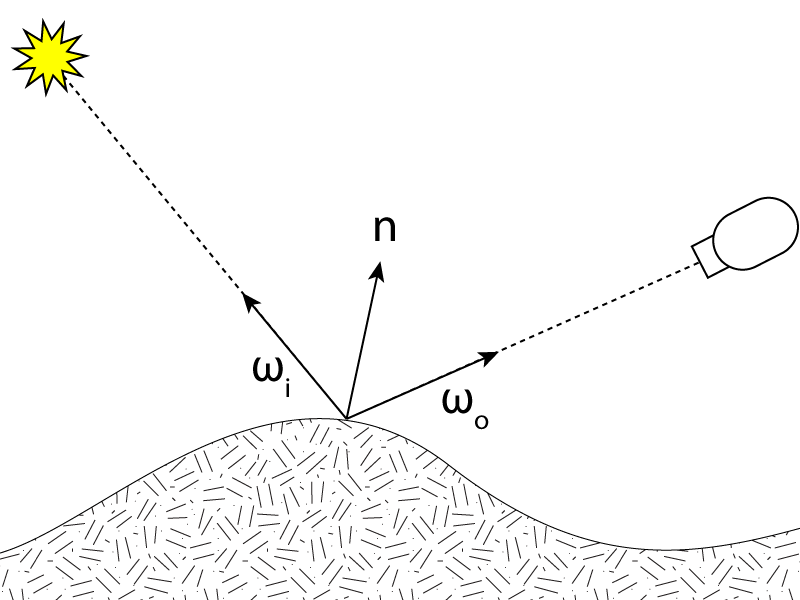
latex/gfx/bitmap/brdfdiagram.png
