sooda/thesis/latex/gfx/bitmap/camerapipeline.png

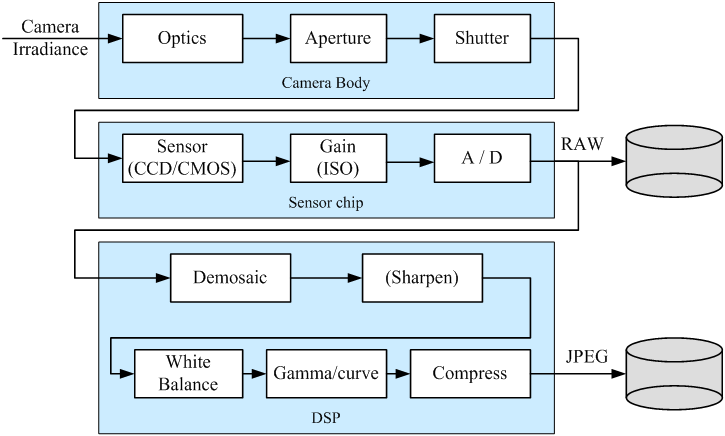
latex/gfx/bitmap/camerapipeline.png
