sooda/thesis/latex/gfx/bitmap/camsremote-proto.jpg

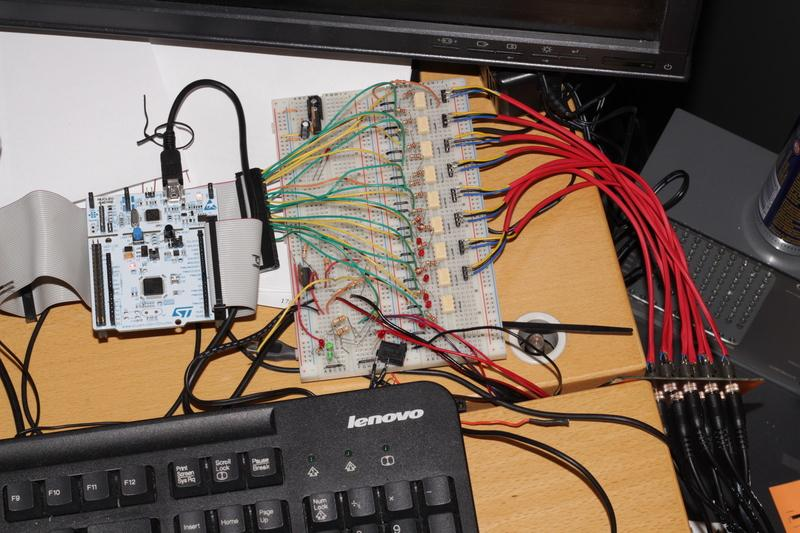
latex/gfx/bitmap/camsremote-proto.jpg
