sooda/thesis/latex/gfx/bitmap/canonef50mm-1.jpg

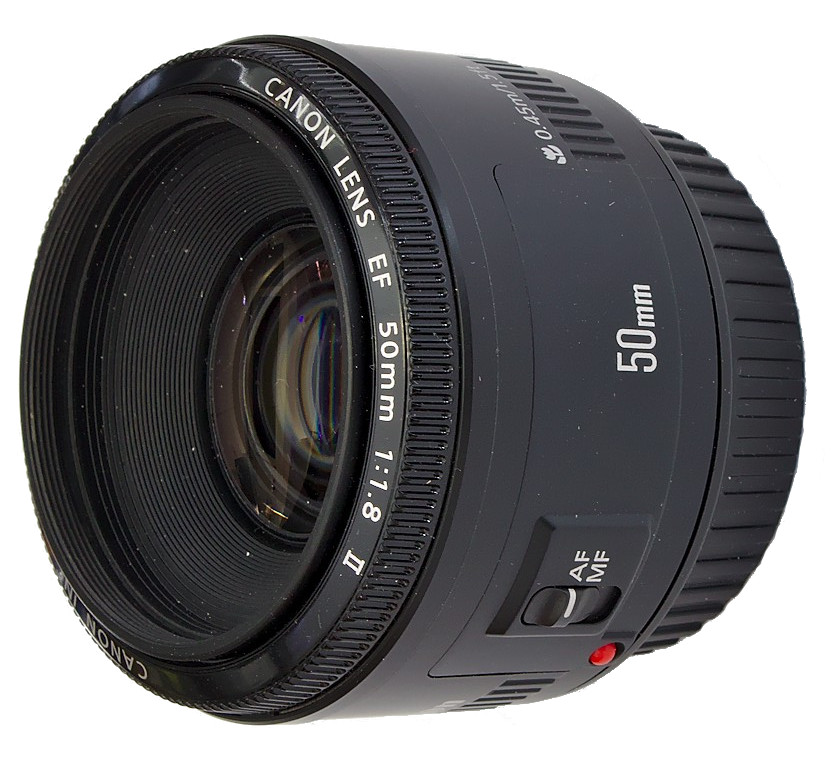
latex/gfx/bitmap/canonef50mm-1.jpg
