sooda/thesis/latex/gfx/bitmap/cases.jpg

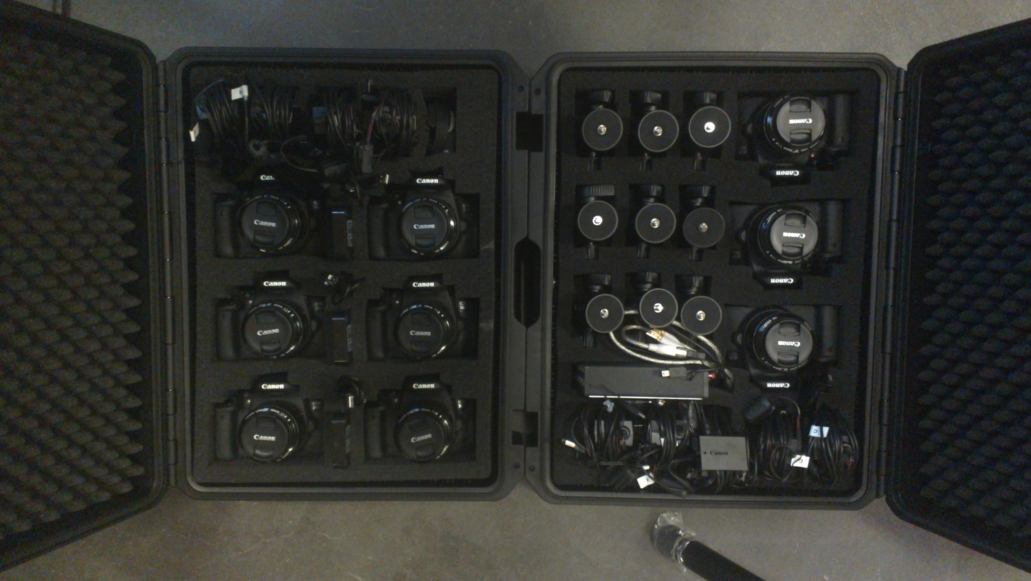
latex/gfx/bitmap/cases.jpg
