sooda/thesis/latex/gfx/bitmap/eos700d.jpg

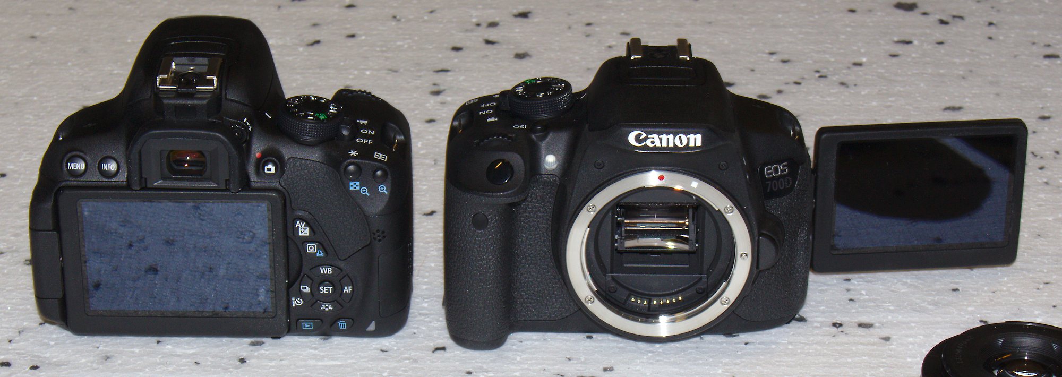
latex/gfx/bitmap/eos700d.jpg
