sooda/thesis/latex/gfx/bitmap/flashtiming-b.jpg

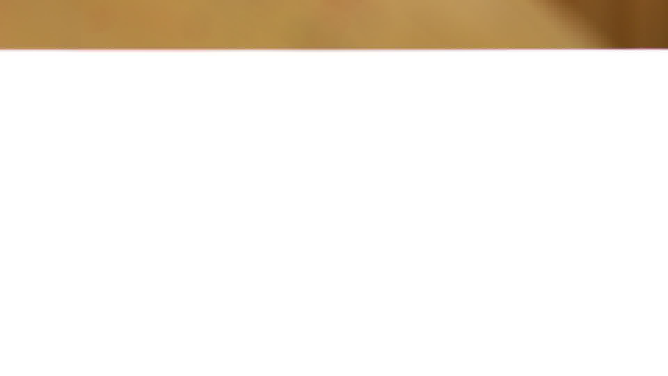
latex/gfx/bitmap/flashtiming-b.jpg
