sooda/thesis/latex/gfx/bitmap/flashtiming-c.jpg

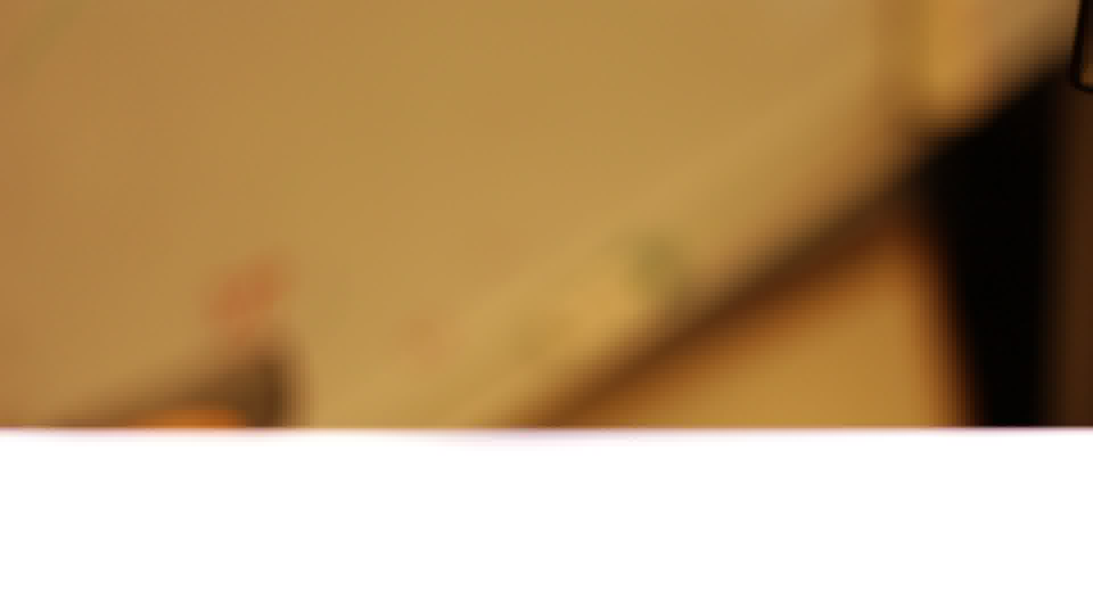
latex/gfx/bitmap/flashtiming-c.jpg
