sooda/thesis/latex/gfx/bitmap/ml-bitrate.png

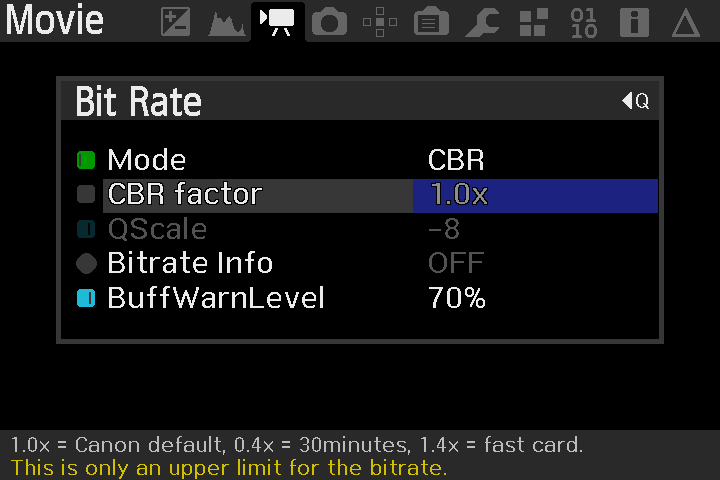
latex/gfx/bitmap/ml-bitrate.png
