sooda/thesis/latex/gfx/bitmap/ml-menu.png

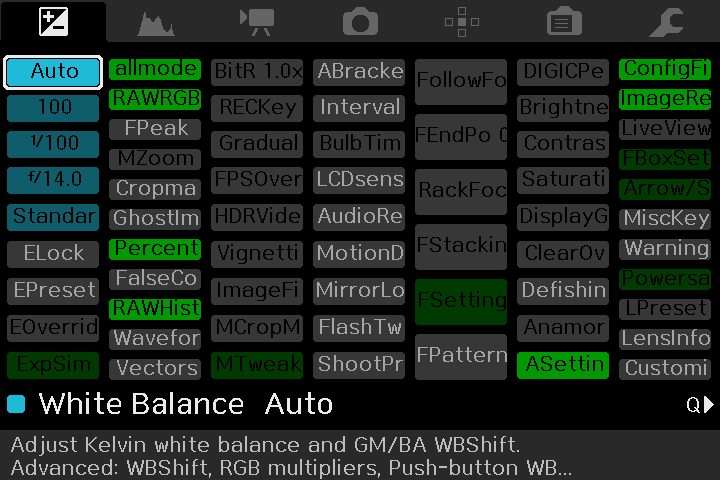
latex/gfx/bitmap/ml-menu.png
