sooda/thesis/latex/gfx/bitmap/nucleo.png

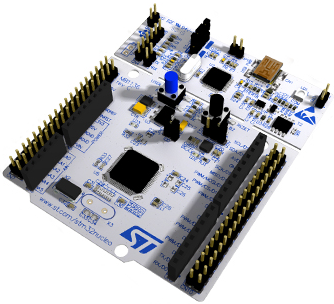
latex/gfx/bitmap/nucleo.png
