sooda/thesis/latex/gfx/bitmap/statue-zoom-mesh.jpg

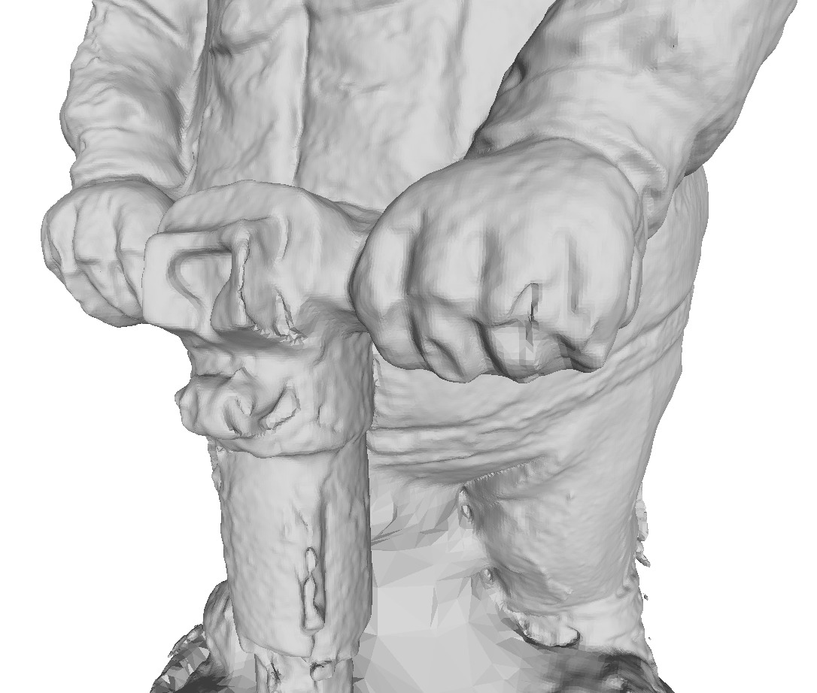
latex/gfx/bitmap/statue-zoom-mesh.jpg
