sooda/thesis/latex/gfx/bitmap/statue-zoom-pts.jpg

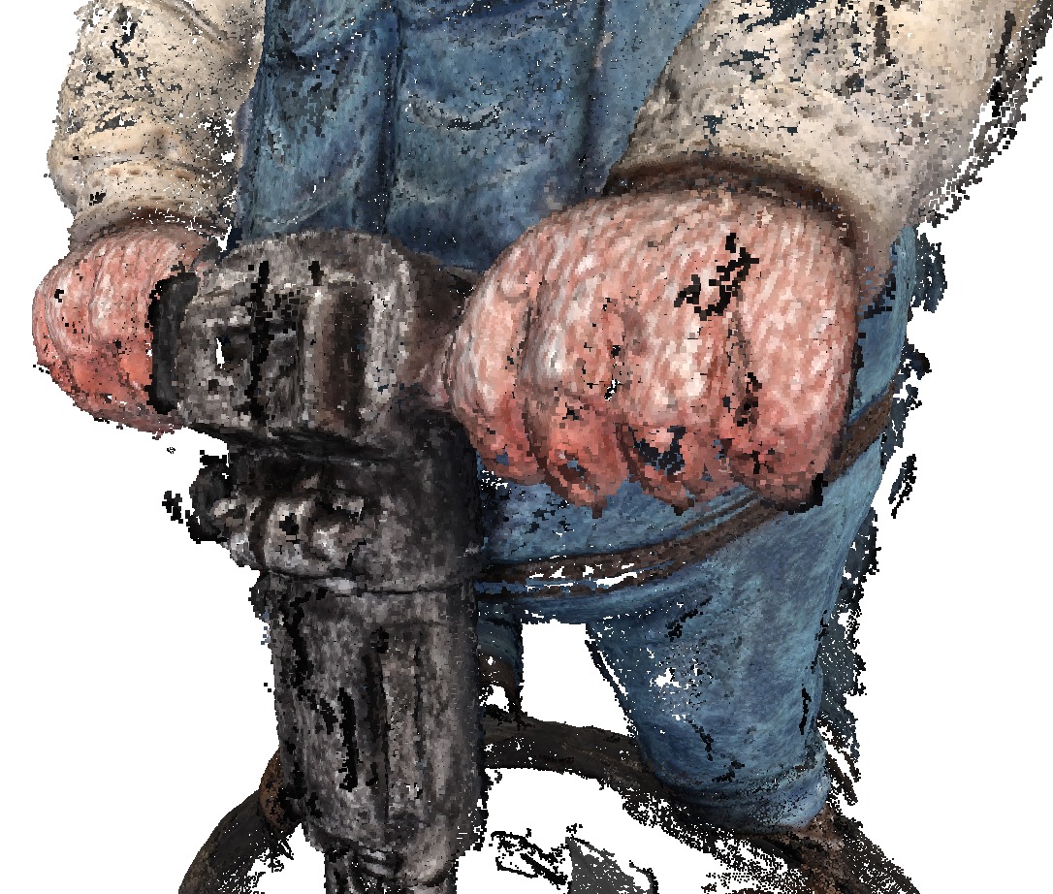
latex/gfx/bitmap/statue-zoom-pts.jpg
