sooda/thesis/semma/presis/gfx/lanoire.jpg

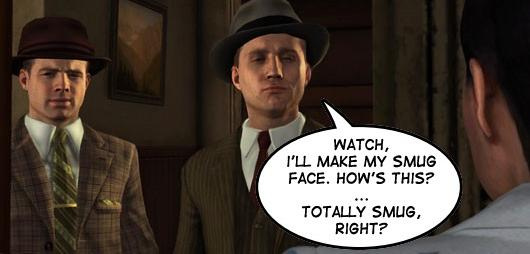
semma/presis/gfx/lanoire.jpg
