sooda/thesis/semma/presis/gfx/lens3.pdf

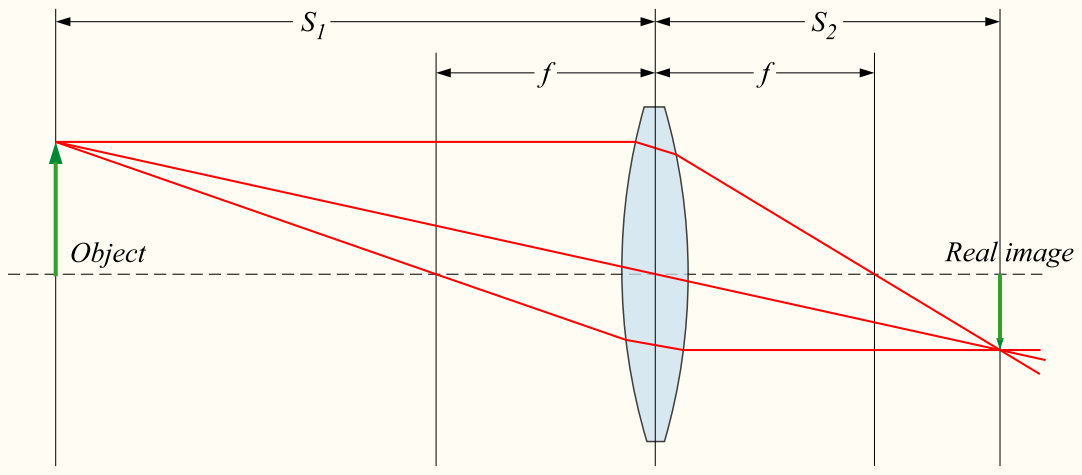
[picture p135: page 1]
